aselectroworks/Analog_Delay/atmel_studio/MainCPU/src/AD5263.h

/*
 * AD5263.h
 *
 * Created: 2014/01/25 16:35:36
 *  Author: A.S
 */ 


#ifndef AD5263_H_
#define AD5263_H_

#define AD5263_BASE_ADR		0x2C
#define AD5263_ADR_PIN 		0x01
#define AD5263_ADR_BYTE		AD5263_BASE_ADR | AD5263_ADR_PIN
#define AD5263_ADR1_BIT		6
#define AD5263_ADR0_BIT		5
#define AD5263_RS_BIT		4
#define AD5263_SD_BIT		3
#define AD5263_O1_BIT		2
#define AD5263_O2_BIT		1



#endif /* AD5263_H_ */
